Amphyby/mozc-devices/mozc-dial/stls/nine_dials/cap_a.stl

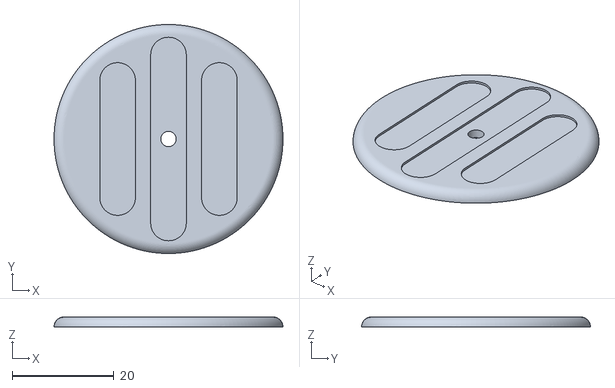
[picture p19: CAD file, 2025-10-28]
mozc-dial/stls/nine_dials/cap_a.stl
45.0 x 45.0 x 2.00
