Amphyby/mozc-devices/mozc-dial/stls/nine_dials/cover_large.stl

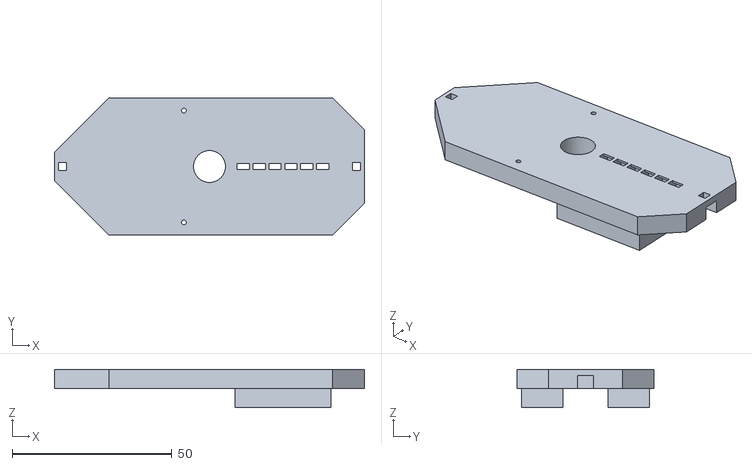
[picture p20: CAD file, 2025-10-28]
mozc-dial/stls/nine_dials/cover_large.stl
97.0 x 43.0 x 12.0
