Amphyby/mozc-devices/mozc-dial/stls/nine_dials/dial_c.stl

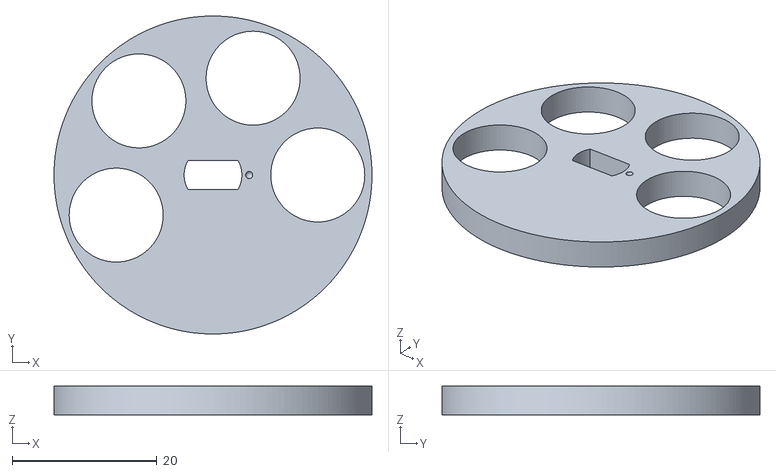
[picture p21: CAD file, 2025-10-28]
mozc-dial/stls/nine_dials/dial_c.stl
44.0 x 44.0 x 4.00
