Amphyby/mozc-devices/mozc-dial/stls/nine_dials/clutch.stl

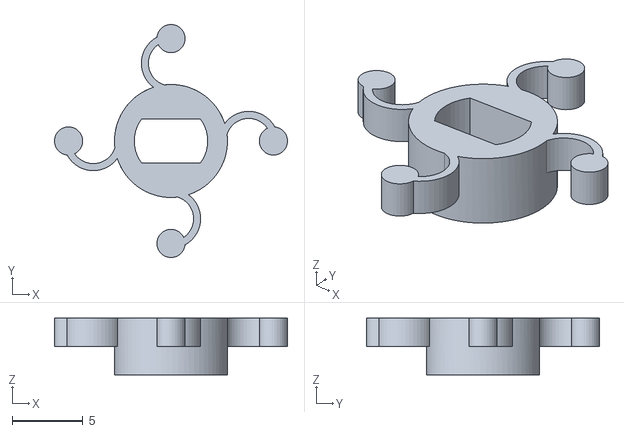
[picture p22: CAD file, 2025-10-28]
mozc-dial/stls/nine_dials/clutch.stl
16.5 x 16.5 x 4.00
