Amphyby/mozc-devices/mozc-dial/stls/nine_dials/encoder_i.stl

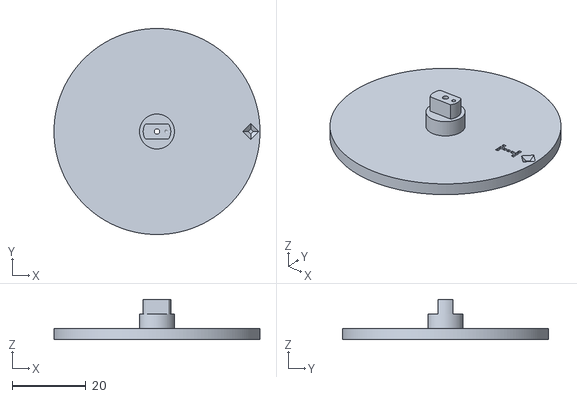
[picture p23: CAD file, 2025-10-28]
mozc-dial/stls/nine_dials/encoder_i.stl
56.0 x 56.0 x 11.0
