Amphyby/mozc-devices/mozc-dial/stls/nine_dials/cover_small.stl

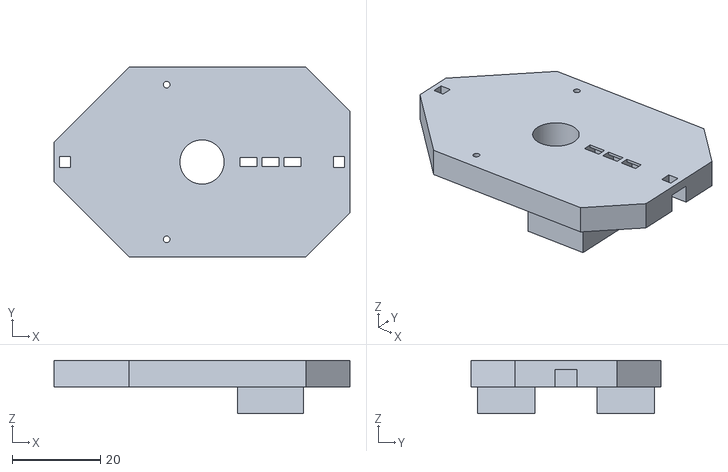
[picture p24: CAD file, 2025-10-28]
mozc-dial/stls/nine_dials/cover_small.stl
67.0 x 43.0 x 12.0
