Amphyby/mozc-devices/mozc-dial/stls/nine_dials/dial_e.stl

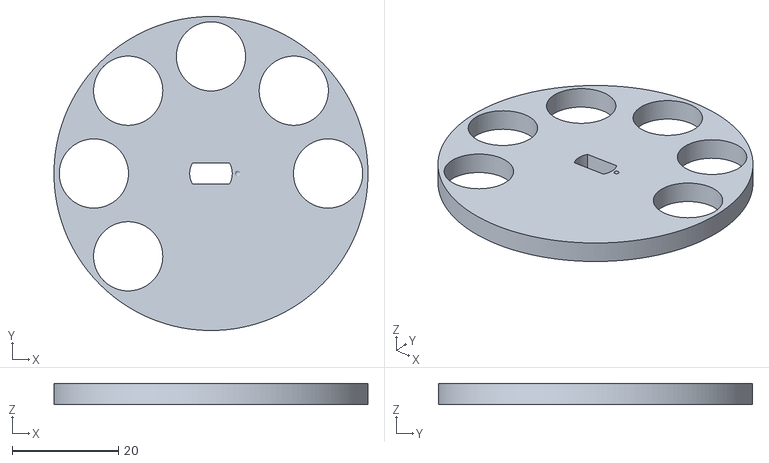
[picture p25: CAD file, 2025-10-28]
mozc-dial/stls/nine_dials/dial_e.stl
59.0 x 59.0 x 4.00
