Amphyby/mozc-devices/mozc-dial/stls/nine_dials/dial_a.stl

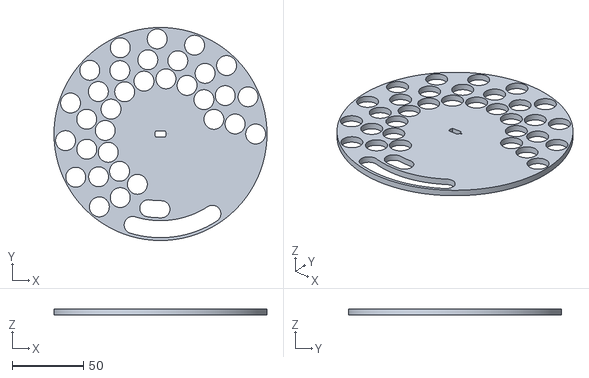
[picture p26: CAD file, 2025-10-28]
mozc-dial/stls/nine_dials/dial_a.stl
150.0 x 150.0 x 4.00
