Amphyby/mozc-devices/mozc-dial/stls/nine_dials/end3.stl

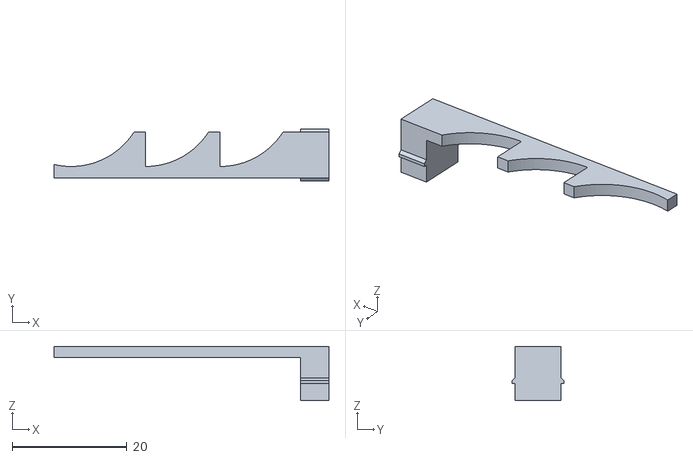
[picture p27: CAD file, 2025-10-28]
mozc-dial/stls/nine_dials/end3.stl
48.0 x 9.00 x 9.50
