Amphyby/mozc-devices/mozc-dial/stls/nine_dials/dial_d.stl

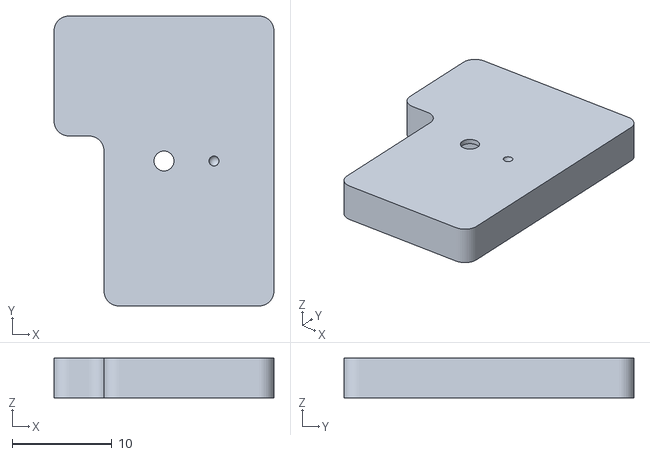
[picture p28: CAD file, 2025-10-28]
mozc-dial/stls/nine_dials/dial_d.stl
22.0 x 29.0 x 4.00
